MOSH-Insa-Toulouse/MOSH_Grau/esquisses_jauges/type_1.png

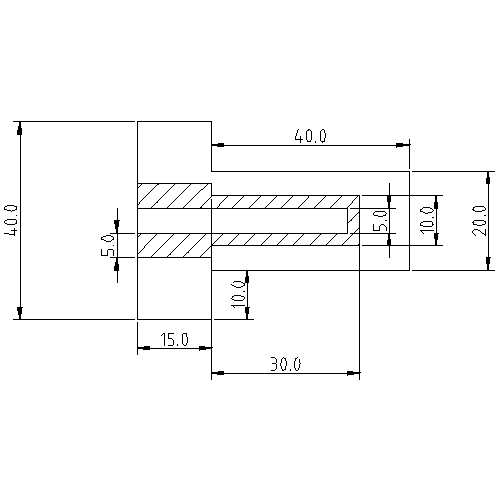
esquisses_jauges/type_1.png
