MOSH-Insa-Toulouse/MOSH_Grau/esquisses_jauges/type_2.png

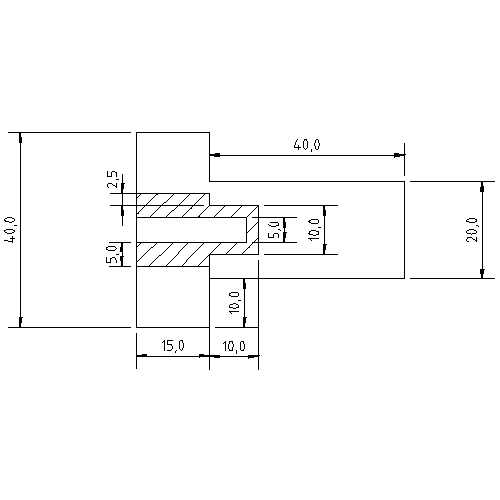
esquisses_jauges/type_2.png
