MOSH-Insa-Toulouse/MOSH_Grau/images/20210505_125856.jpg

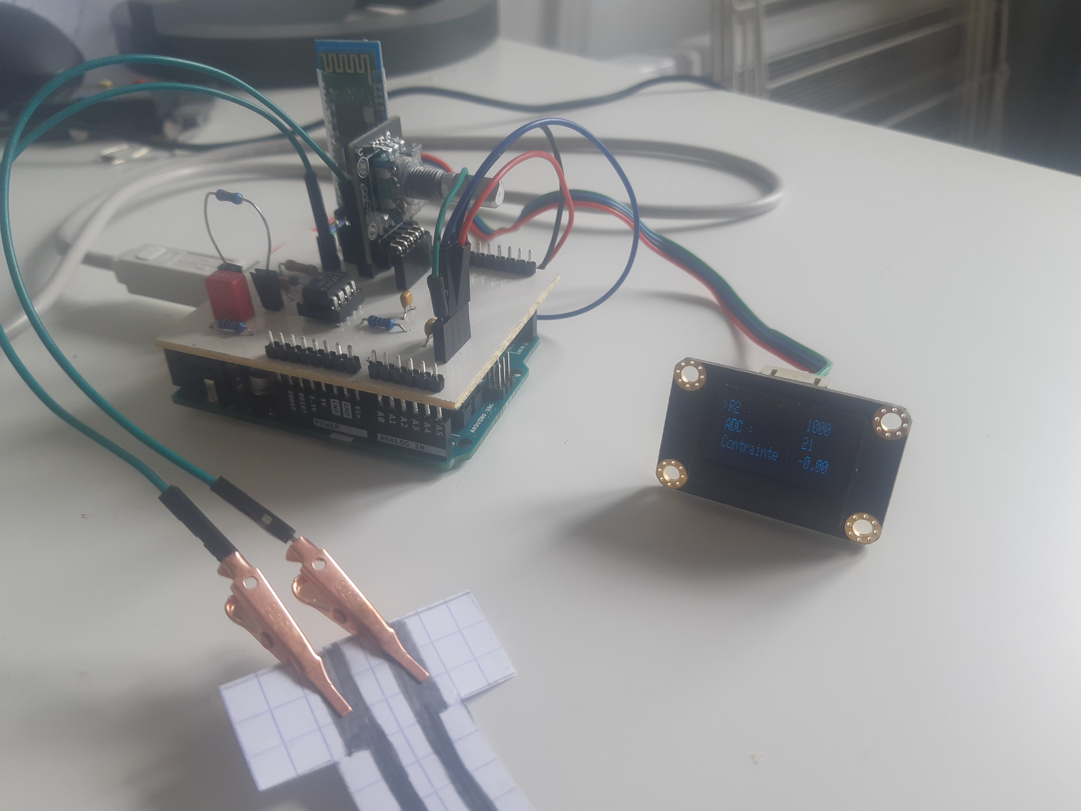
images/20210505_125856.jpg
