MOSH-Insa-Toulouse/MOSH_Grau/images/20210505_125911.jpg

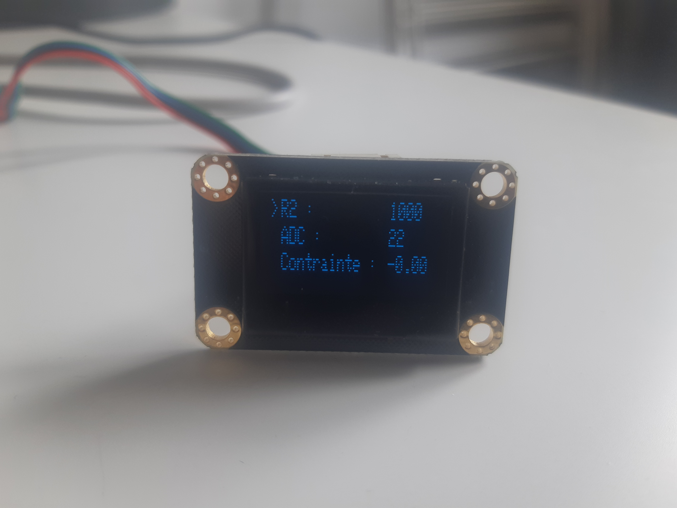
images/20210505_125911.jpg
