MOSH-Insa-Toulouse/MOSH_Grau/images/20210505_131032.jpg

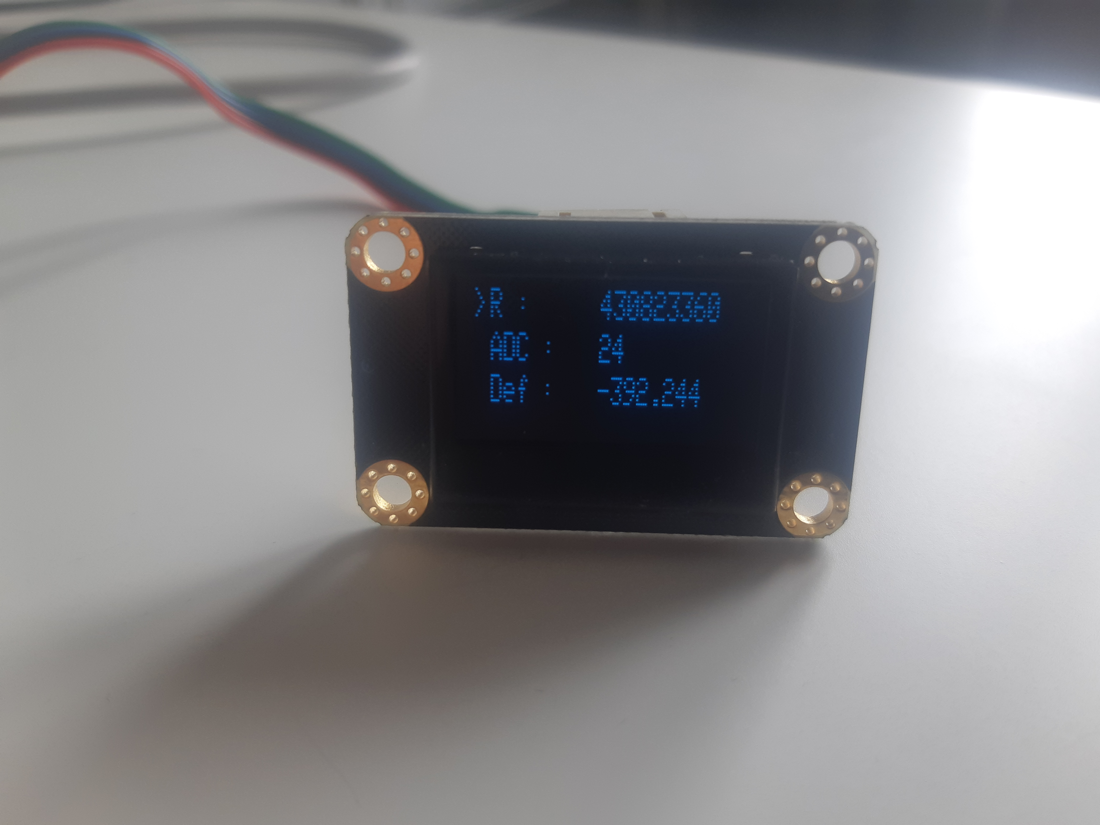
images/20210505_131032.jpg
