MOSH-Insa-Toulouse/MOSH_Grau/images/20210505_131059.jpg

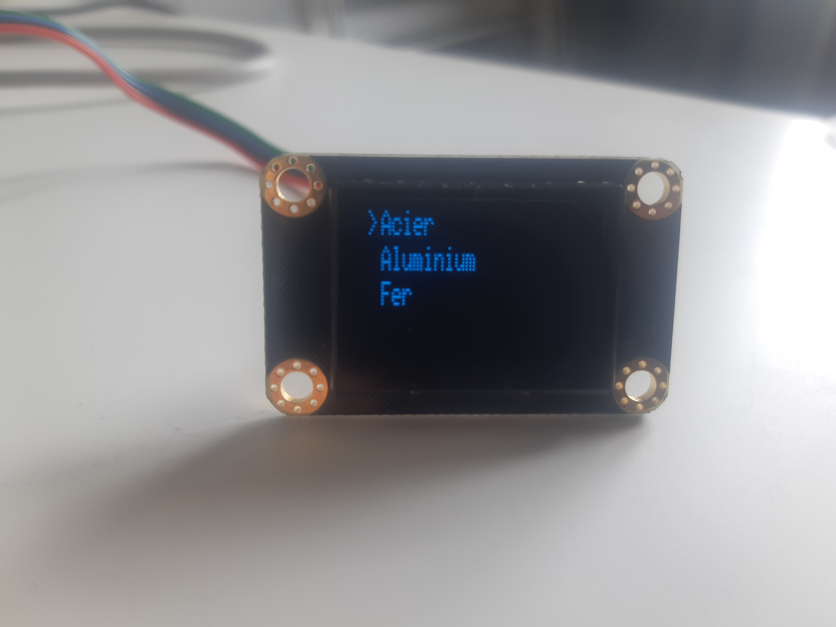
images/20210505_131059.jpg
