MOSH-Insa-Toulouse/MOSH_Grau/Résultats/21-04_HB_180.png

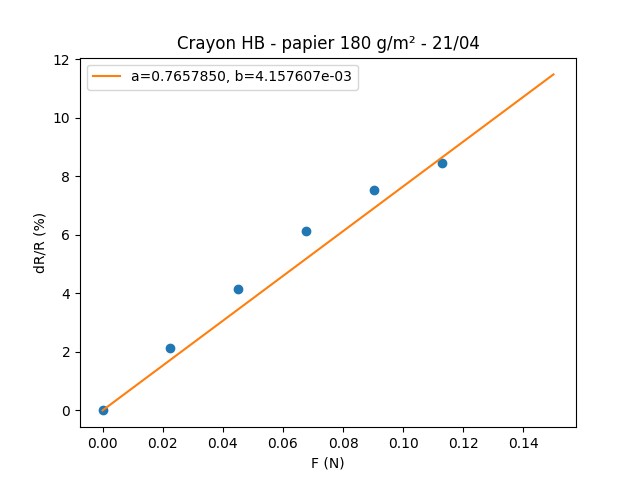
Résultats/21-04_HB_180.png
