MOSH-Insa-Toulouse/MOSH_Grau/Résultats/graph_80g_4H_comp.png

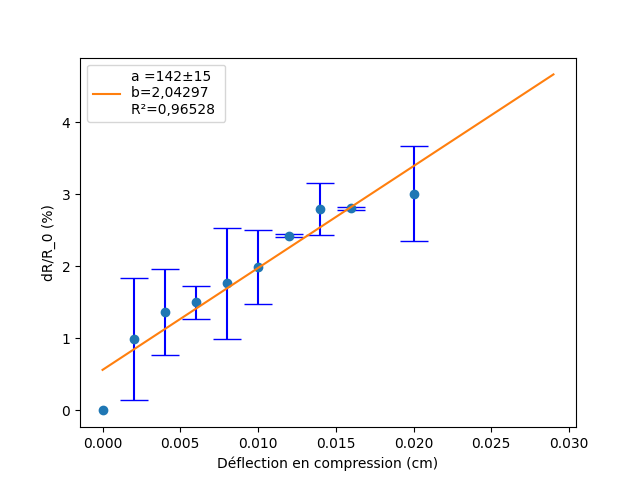
Résultats/graph_80g_4H_comp.png
