MOSH-Insa-Toulouse/MOSH_Grau/Résultats/graph_180g_4H_comp.png

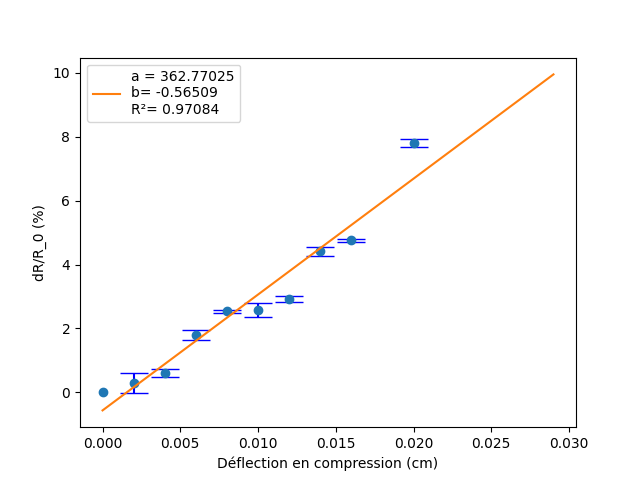
Résultats/graph_180g_4H_comp.png
