MOSH-Insa-Toulouse/MOSH_Grau/Résultats/sensi_VS_R0_205g_HB.png

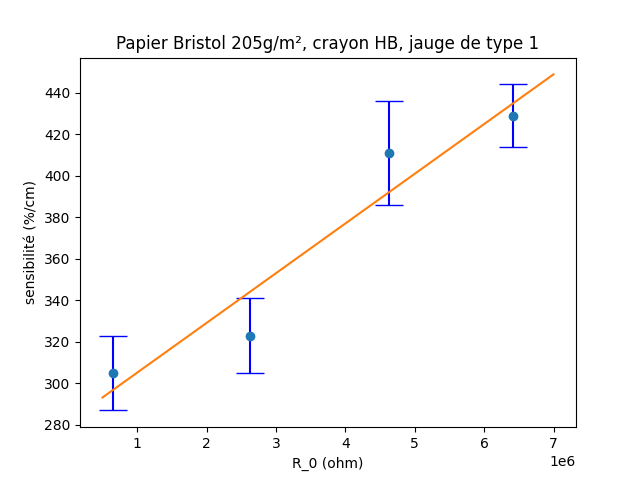
Résultats/sensi_VS_R0_205g_HB.png
