MOSH-Insa-Toulouse/MOSH_Grau/Résultats/tab_205g_HB_comp.png

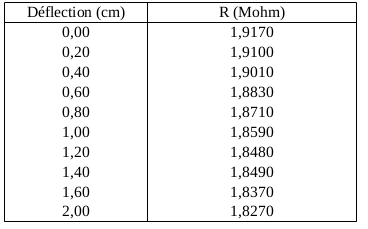
Résultats/tab_205g_HB_comp.png
