MOSH-Insa-Toulouse/MOSH_Grau/Résultats/tensionVSr.png

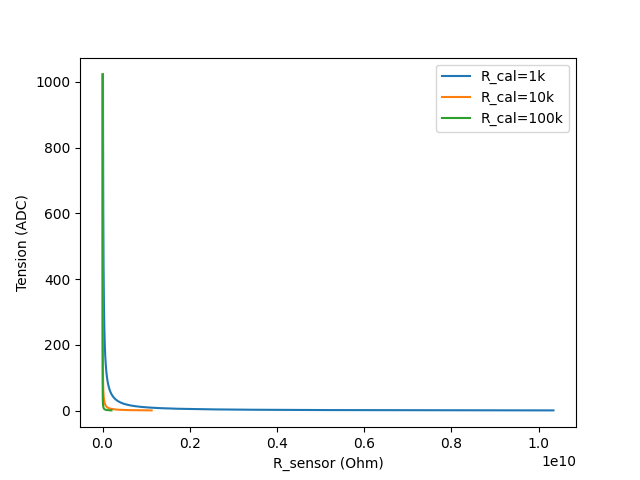
Résultats/tensionVSr.png
