MOSH-Insa-Toulouse/MOSH_Grau/Résultats/tensionVSr_zoom.png

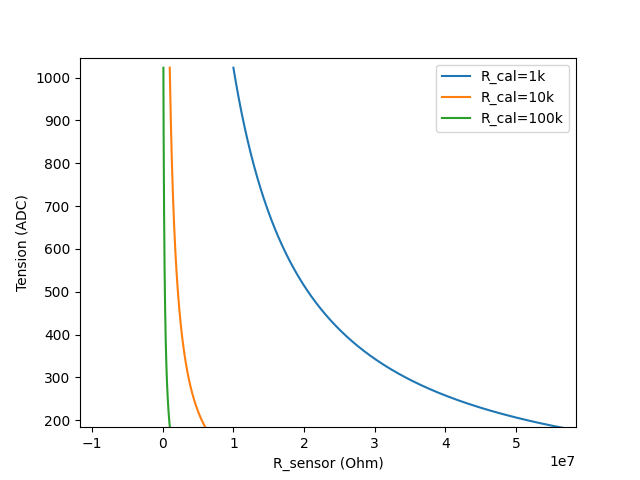
Résultats/tensionVSr_zoom.png
